MemphisOmar/Scara-arm-with-GUI/SCARA_CAD/GRIPPER/images/IMG_7484.JPG

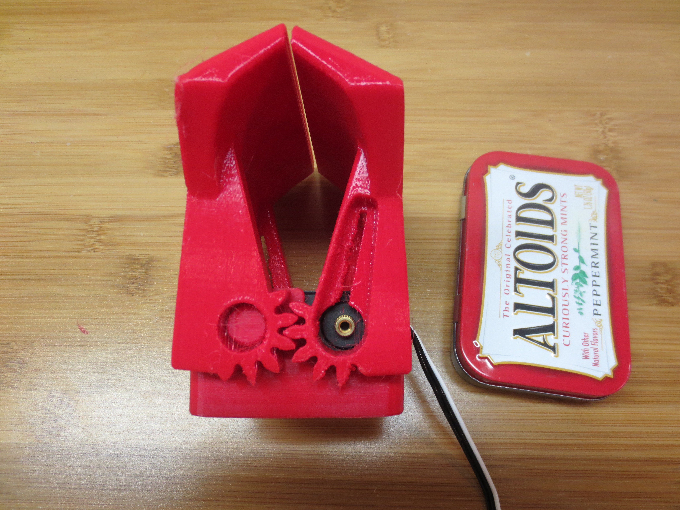
SCARA_CAD/GRIPPER/images/IMG_7484.JPG
