MemphisOmar/Scara-arm-with-GUI/SCARA_CAD/Thrust Bearing 35x52x12mm.SLDPRT

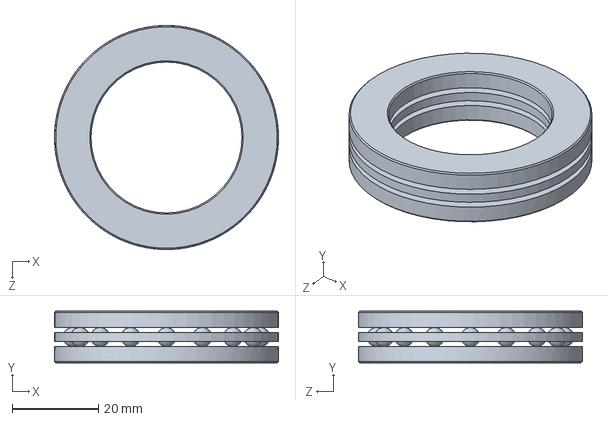
[picture p21: CAD file, 2024-12-12]
SCARA_CAD/Thrust Bearing 35x52x12mm.SLDPRT
52.0 x 12.0 x 52.0 mm
