MemphisOmar/Scara-arm-with-GUI/SCARA_CAD/Ball Bearing 35x47x7mm.SLDPRT

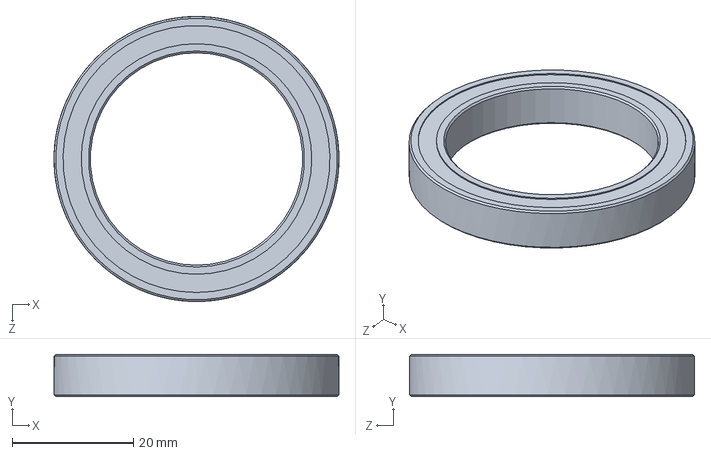
[picture p22: CAD file, 2024-12-12]
SCARA_CAD/Ball Bearing 35x47x7mm.SLDPRT
47.0 x 7.00 x 47.0 mm
