MemphisOmar/Scara-arm-with-GUI/SCARA_CAD/Micro switch.SLDPRT

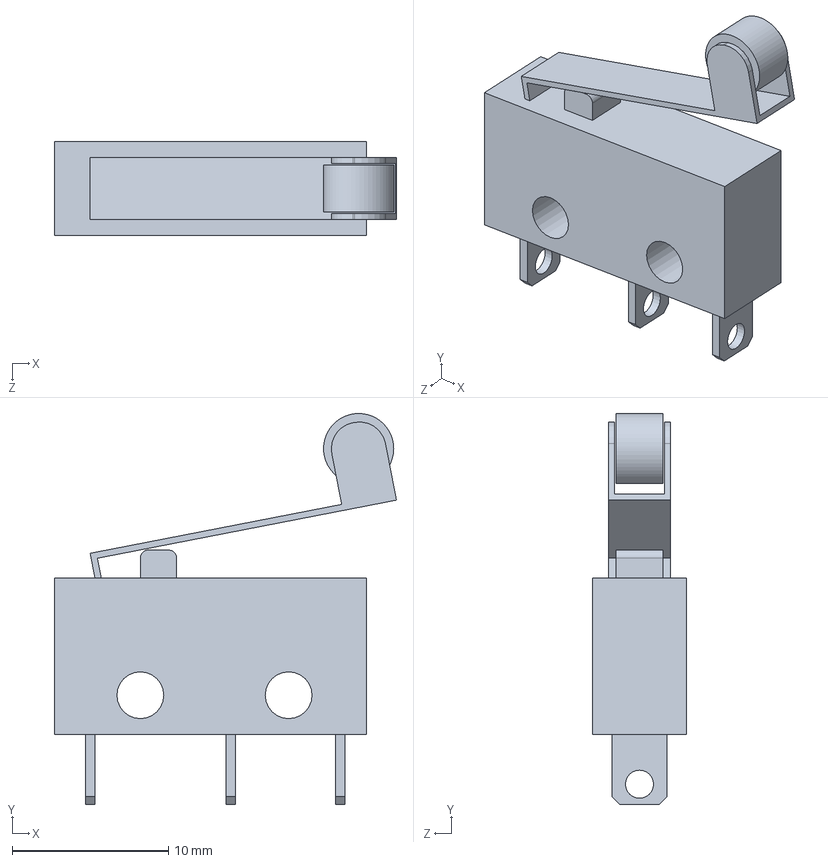
[picture p23: CAD file, 2024-12-12]
SCARA_CAD/Micro switch.SLDPRT
21.9 x 25.0 x 6.00 mm
