MemphisOmar/Scara-arm-with-GUI/SCARA_CAD/Smooth Rod D10mm L400mm.SLDPRT

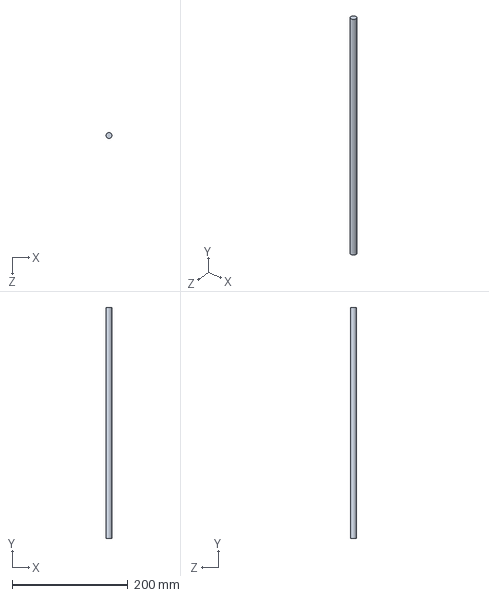
[picture p24: CAD file, 2024-12-12]
SCARA_CAD/Smooth Rod D10mm L400mm.SLDPRT
10.0 x 400.0 x 10.0 mm
