MemphisOmar/Scara-arm-with-GUI/SCARA_CAD/Ball Bearing 30x42x7mm.SLDPRT

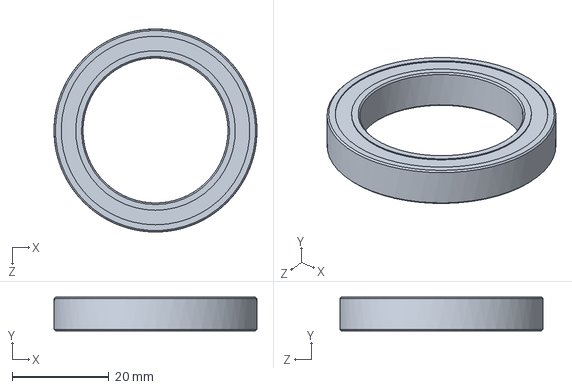
[picture p25: CAD file, 2024-12-12]
SCARA_CAD/Ball Bearing 30x42x7mm.SLDPRT
42.0 x 7.00 x 42.0 mm
