MemphisOmar/Scara-arm-with-GUI/SCARA_CAD/GT2 Belt 300mm 2.SLDPRT

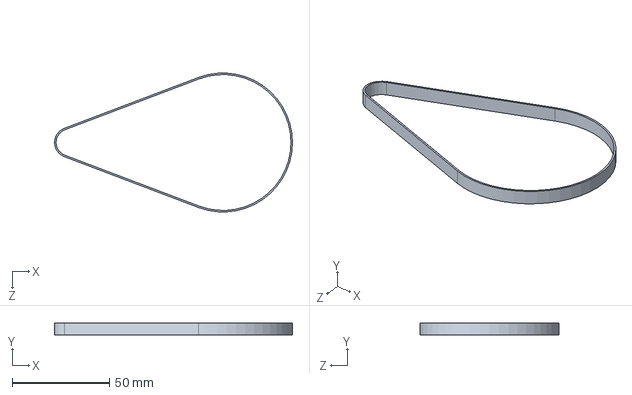
[picture p26: CAD file, 2024-12-12]
SCARA_CAD/GT2 Belt 300mm 2.SLDPRT
122.6 x 6.00 x 71.5 mm
