MemphisOmar/Scara-arm-with-GUI/SCARA_CAD/Stepper NEMA 17 -  20mm shaft.SLDPRT

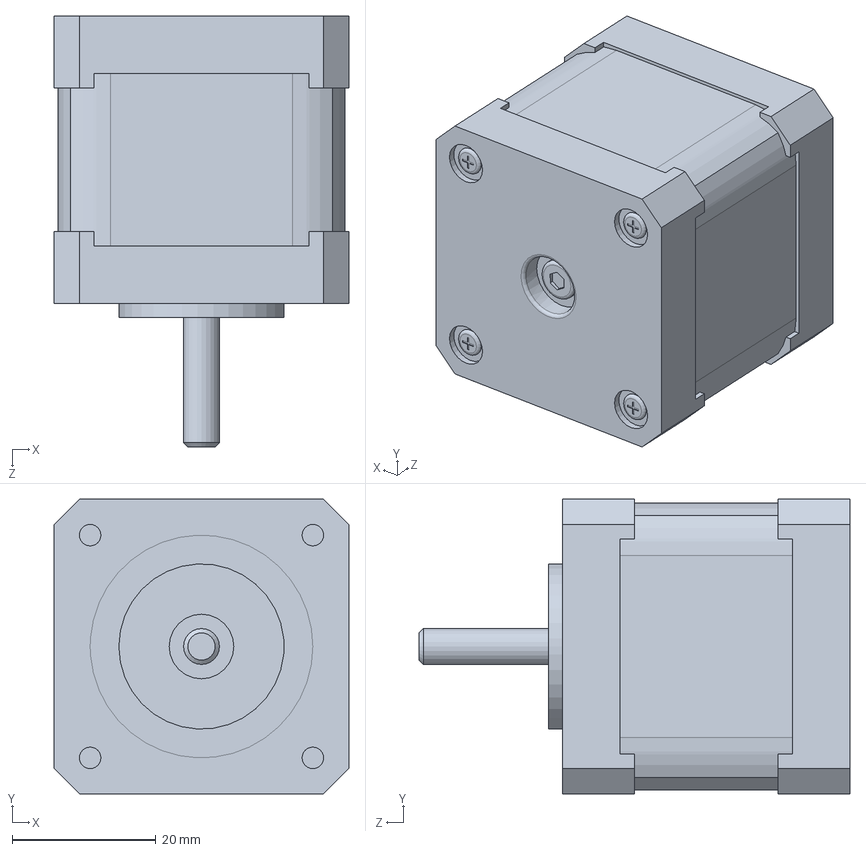
[picture p27: CAD file, 2024-12-12]
SCARA_CAD/Stepper NEMA 17 - 20mm shaft.SLDPRT
41.0 x 41.0 x 60.0 mm
