MemphisOmar/Scara-arm-with-GUI/SCARA_CAD/7-J2TAPABRZO.SLDPRT

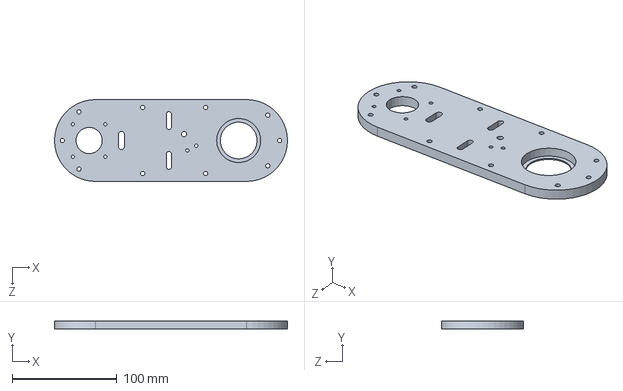
[picture p28: CAD file, 2024-12-12]
SCARA_CAD/7-J2TAPABRZO.SLDPRT
222.0 x 8.00 x 78.0 mm
