MemphisOmar/Scara-arm-with-GUI/SCARA_CAD/4-J1CENTRALBRAZO.SLDPRT

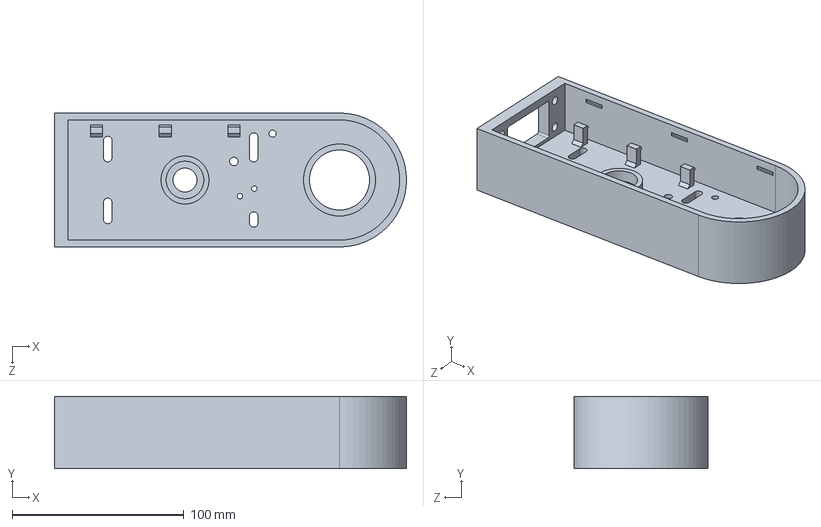
[picture p29: CAD file, 2024-12-12]
SCARA_CAD/4-J1CENTRALBRAZO.SLDPRT
205.0 x 42.0 x 78.0 mm
