MemphisOmar/Scara-arm-with-GUI/SCARA_CAD/5-COPLEJ1J2.SLDPRT

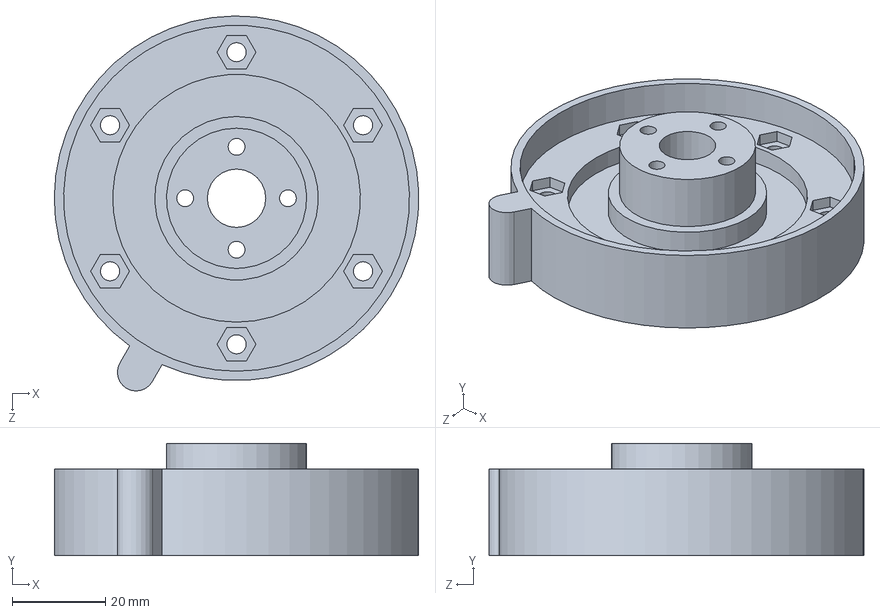
[picture p30: CAD file, 2024-12-12]
SCARA_CAD/5-COPLEJ1J2.SLDPRT
78.0 x 24.0 x 80.2 mm
