MemphisOmar/Scara-arm-with-GUI/SCARA_CAD/8-J3COPLE.SLDPRT

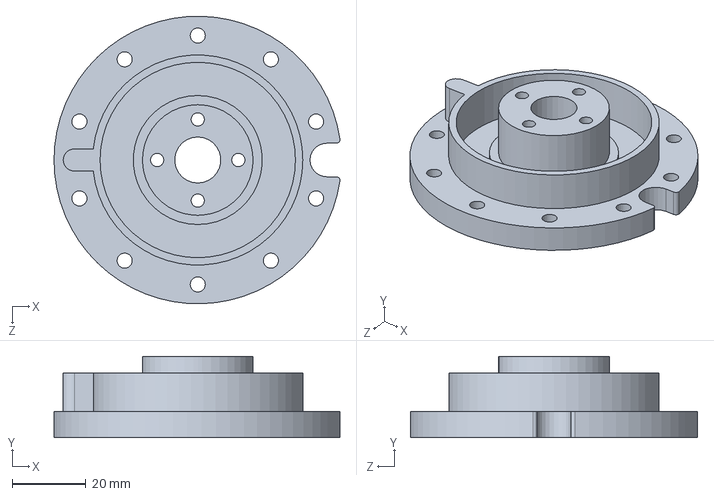
[picture p31: CAD file, 2024-12-12]
SCARA_CAD/8-J3COPLE.SLDPRT
77.6 x 22.0 x 78.0 mm
