MemphisOmar/Scara-arm-with-GUI/SCARA_CAD/GT2 Belt 200mm.SLDPRT

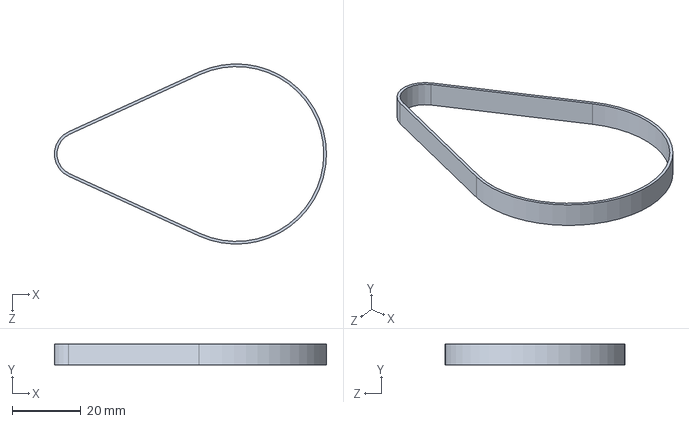
[picture p32: CAD file, 2024-12-12]
SCARA_CAD/GT2 Belt 200mm.SLDPRT
79.4 x 6.00 x 52.6 mm
