MemphisOmar/Scara-arm-with-GUI/SCARA_CAD/0-Base.SLDPRT

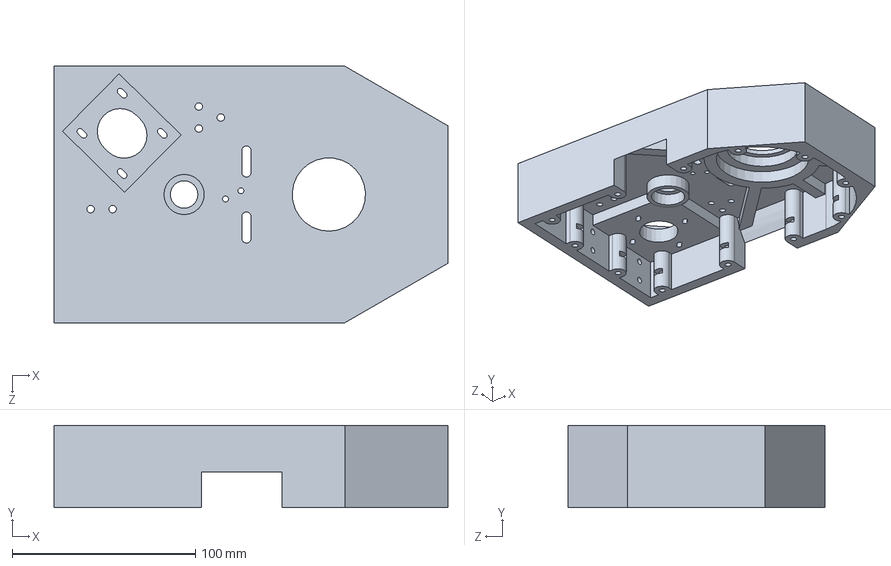
[picture p33: CAD file, 2024-12-12]
SCARA_CAD/0-Base.SLDPRT
215.0 x 45.0 x 140.0 mm
