MemphisOmar/Scara-arm-with-GUI/SCARA_CAD/gearheads-gripper-mount.SLDPRT

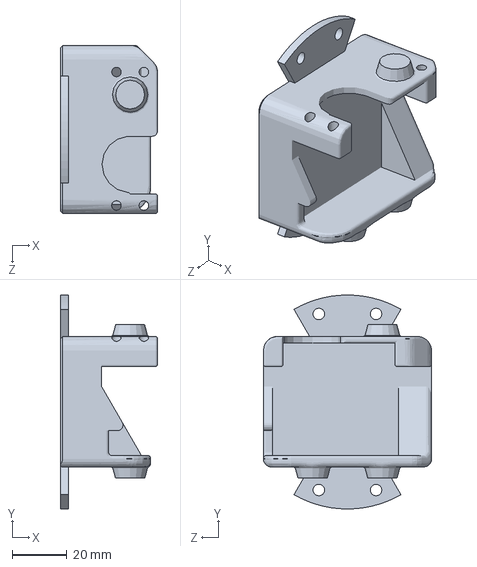
[picture p34: CAD file, 2024-12-12]
SCARA_CAD/gearheads-gripper-mount.SLDPRT
35.4 x 78.0 x 61.3 mm
