MemphisOmar/Scara-arm-with-GUI/SCARA_CAD/2-TapaZ.SLDPRT

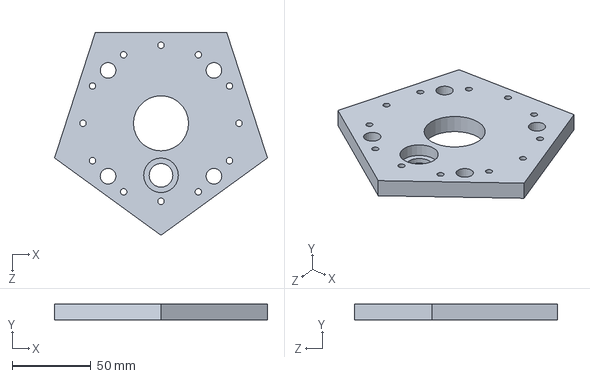
[picture p35: CAD file, 2024-12-12]
SCARA_CAD/2-TapaZ.SLDPRT
135.2 x 10.0 x 128.6 mm
