MemphisOmar/Scara-arm-with-GUI/SCARA_CAD/1-J1 ACOPLEMOD.SLDPRT

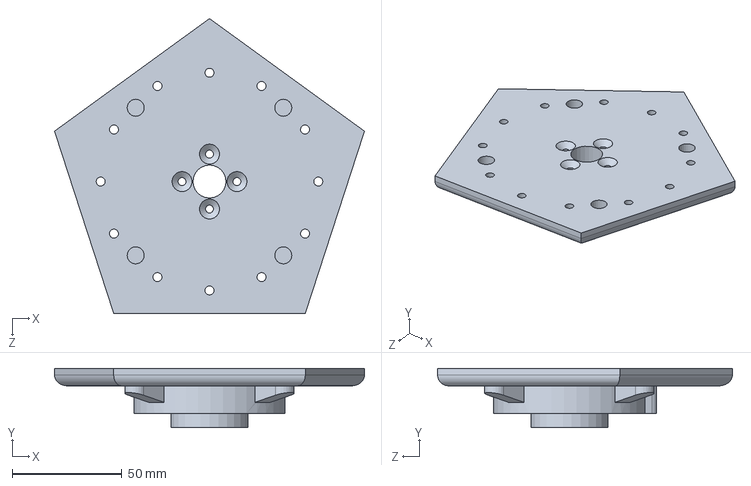
[picture p36: CAD file, 2024-12-12]
SCARA_CAD/1-J1 ACOPLEMOD.SLDPRT
141.1 x 27.0 x 134.2 mm
