MemphisOmar/Scara-arm-with-GUI/SCARA_CAD/Thrust Bearing - 40x60x13.SLDPRT

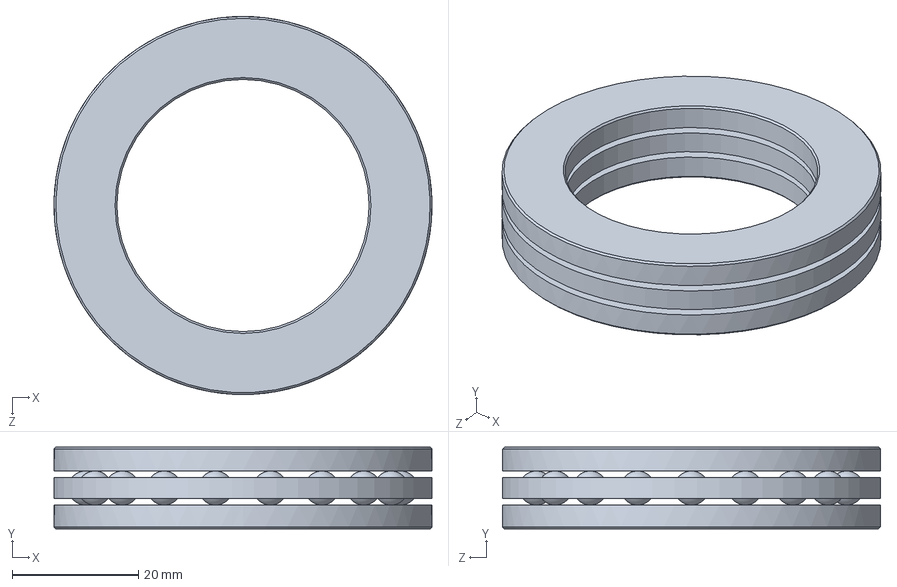
[picture p37: CAD file, 2024-12-12]
SCARA_CAD/Thrust Bearing - 40x60x13.SLDPRT
60.0 x 13.0 x 60.0 mm
